jfcliche/EEMON42/software/embedded/font.py

# pitch = 8x8, font_petme128_8x8.h from micropython framebuf module
# https://github.com/micropython/micropython/blob/master/extmod/font_petme128_8x8.h
font8x8 = memoryview(bytes(( 
    
    # Placeholder for chars 0-31. Encoded horizontally, so not valid
    0x00, 0x00, 0x00, 0x00, 0x00, 0x00, 0x00, 0x00,  # 0000 (uni0000.dup1)
    0x7e, 0x81, 0xa5, 0x81, 0xbd, 0x99, 0x81, 0x7e,  # 0001 (uni0001)
    0x7e, 0xff, 0xdb, 0xff, 0xc3, 0xe7, 0xff, 0x7e,  # 0002 (uni0002)
    0x6c, 0xfe, 0xfe, 0xfe, 0x7c, 0x38, 0x10, 0x00,  # 0003 (uni0003)
    0x10, 0x38, 0x7c, 0xfe, 0x7c, 0x38, 0x10, 0x00,  # 0004 (uni0004)
    0x38, 0x7c, 0x38, 0xfe, 0xfe, 0x7c, 0x38, 0x7c,  # 0005 (uni0005)
    0x10, 0x10, 0x38, 0x7c, 0xfe, 0x7c, 0x38, 0x7c,  # 0006 (uni0006)
    0x00, 0x00, 0x18, 0x3c, 0x3c, 0x18, 0x00, 0x00,  # 0007 (uni0007)
    0xff, 0xff, 0xe7, 0xc3, 0xc3, 0xe7, 0xff, 0xff,  # 0008 (uni0008)
    0x00, 0x3c, 0x66, 0x42, 0x42, 0x66, 0x3c, 0x00,  # 0009 (uni0009)
    0xff, 0xc3, 0x99, 0xbd, 0xbd, 0x99, 0xc3, 0xff,  # 000a (uni000A)
    0x0f, 0x07, 0x0f, 0x7d, 0xcc, 0xcc, 0xcc, 0x78,  # 000b (uni000B)
    0x3c, 0x66, 0x66, 0x66, 0x3c, 0x18, 0x7e, 0x18,  # 000c (uni000C)
    0x3f, 0x33, 0x3f, 0x30, 0x30, 0x70, 0xf0, 0xe0,  # 000d (uni000D)
    0x7f, 0x63, 0x7f, 0x63, 0x63, 0x67, 0xe6, 0xc0,  # 000e (uni000E)
    0x99, 0x5a, 0x3c, 0xe7, 0xe7, 0x3c, 0x5a, 0x99,  # 000f (uni000F)
    0x80, 0xe0, 0xf8, 0xfe, 0xf8, 0xe0, 0x80, 0x00,  # 0010 (uni0010)
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
0x1c,0x20,0x20,0x3c,0x00,
0x1c,0x20,0x1c,0x00,0x00,
0x3c,0x30,0x30,0x3c,0x00,
0x24,0x18,0x18,0x24,0x00,
0x0c,0x50,0x20,0x1c,0x00,
0x24,0x34,0x2c,0x24,0x00,
0x04,0x1e,0x21,0x00,0x00,
0x00,0x3f,0x00,0x00,0x00,
0x21,0x1e,0x04,0x00,0x00,
0x02,0x01,0x02,0x01,0x00,
0x00,0x00,0x00,0x00,0x00,
)))
